ThomasBirkmaier/trek-emonda-tavelo-spacer-adapter/01_Input/2026-09-28_Tavelo-Adapter_auf_Trek-Deckel.jpg

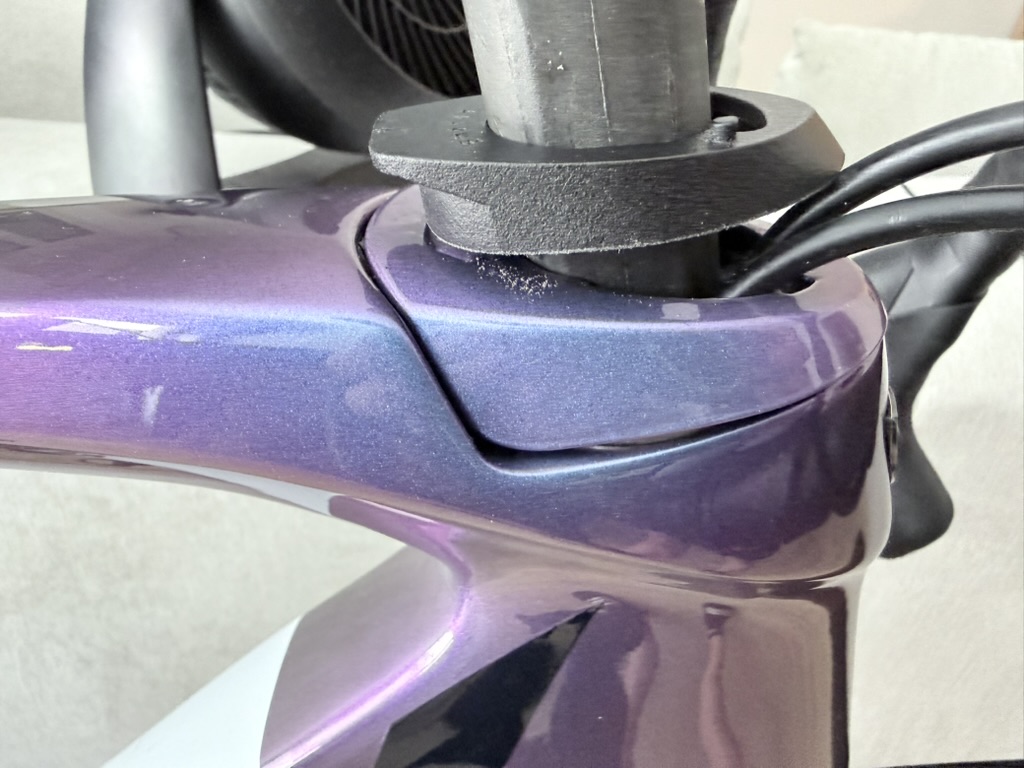
01_Input/2026-09-28_Tavelo-Adapter_auf_Trek-Deckel.jpg
