ThomasBirkmaier/trek-emonda-tavelo-spacer-adapter/01_Input/2026-09-28_Tavelo-Spacer_Teilung_IMG_8871.jpg

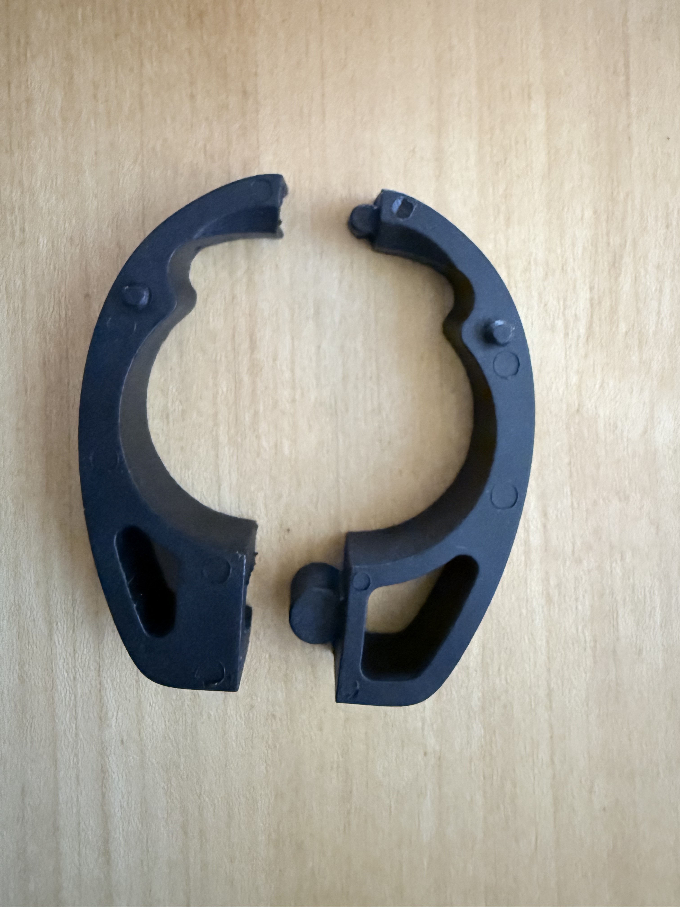
01_Input/2026-09-28_Tavelo-Spacer_Teilung_IMG_8871.jpg
