ThomasBirkmaier/trek-emonda-tavelo-spacer-adapter/01_Input/2026-09-28_Trek-Cockpit_original_seitlich.jpg

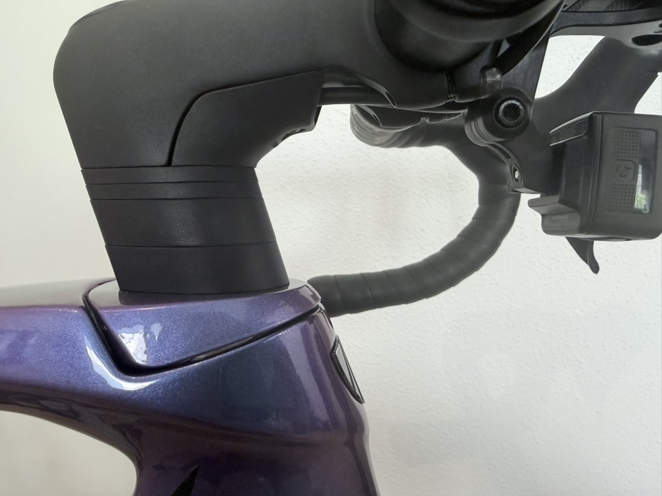
01_Input/2026-09-28_Trek-Cockpit_original_seitlich.jpg
