ThomasBirkmaier/trek-emonda-tavelo-spacer-adapter/01_Input/2026-09-28_Trek-Deckel_Nasen_Leitungsoeffnung.jpg

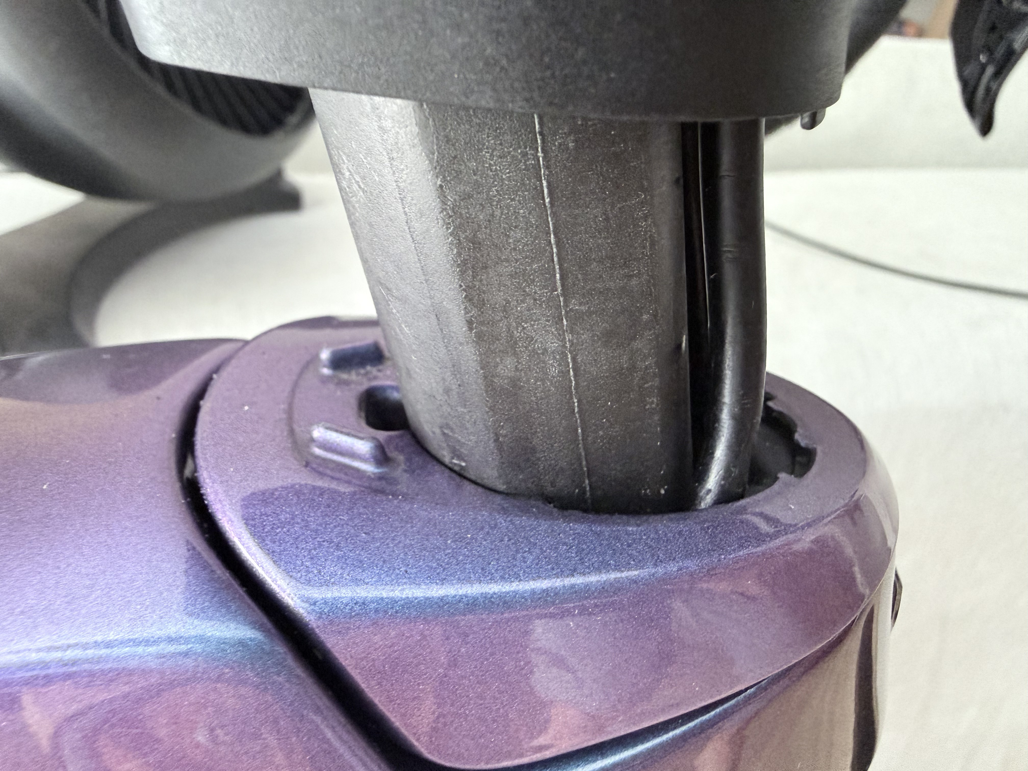
01_Input/2026-09-28_Trek-Deckel_Nasen_Leitungsoeffnung.jpg
