ThomasBirkmaier/trek-emonda-tavelo-spacer-adapter/01_Input/2026-09-28_Trek-Vorbau_angehoben_seitlich_2.jpg

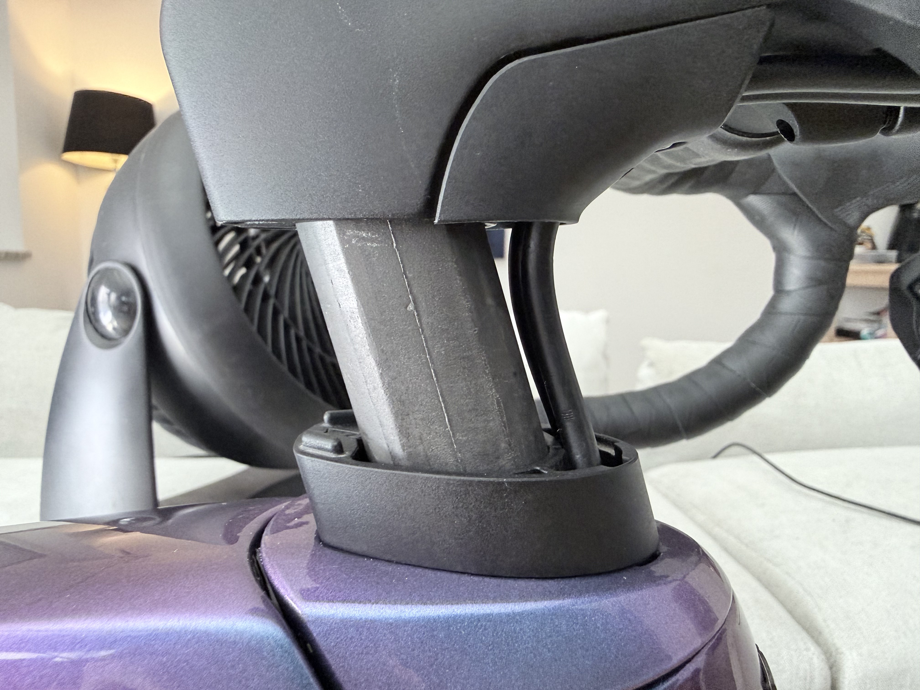
01_Input/2026-09-28_Trek-Vorbau_angehoben_seitlich_2.jpg
