ThomasBirkmaier/trek-emonda-tavelo-spacer-adapter/03_Renderings/Drucklayout_Adapter.png

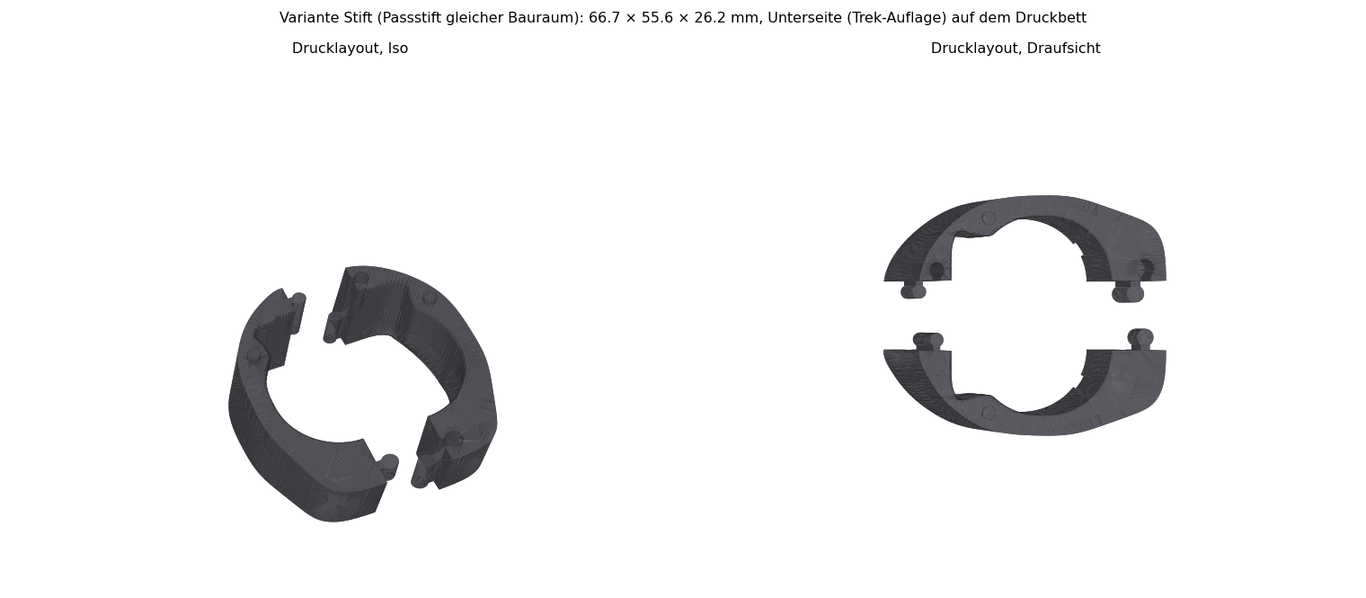
03_Renderings/Drucklayout_Adapter.png
